Maniak003/Meteostation/Documents/IMG_20230122_160000.png

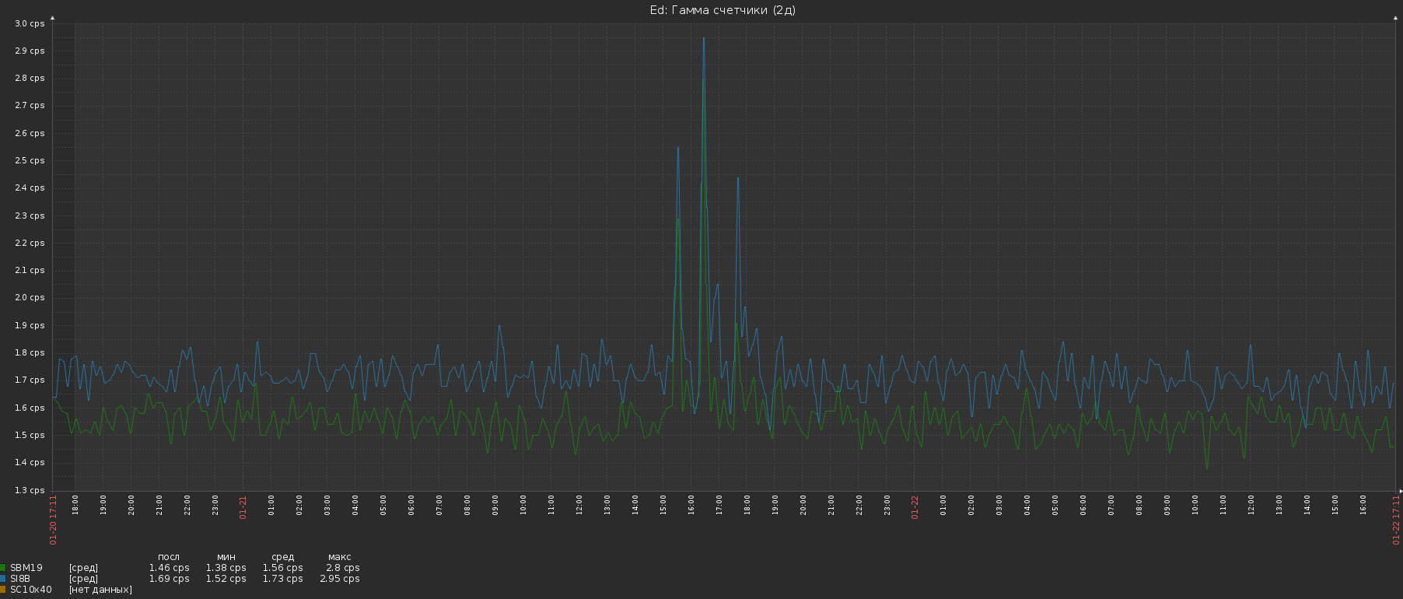
Documents/IMG_20230122_160000.png
