Maniak003/Meteostation/Documents/IMG_20230129_122235.jpg

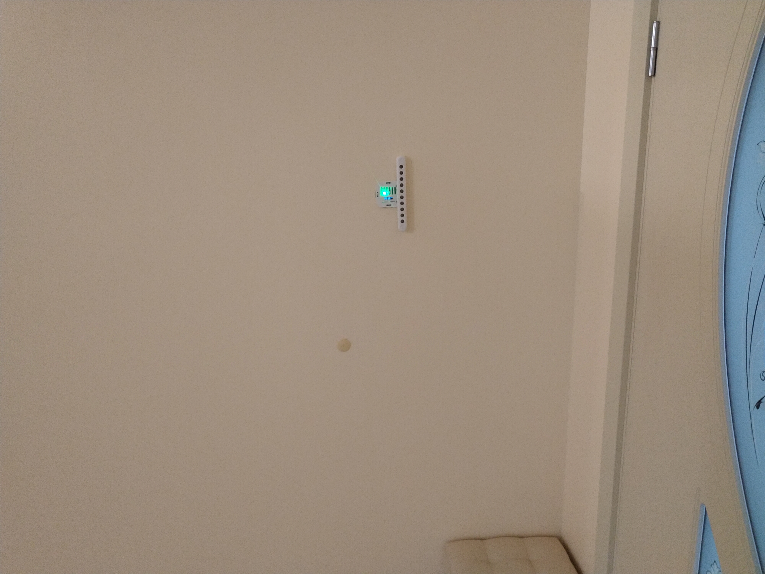
Documents/IMG_20230129_122235.jpg
