Maniak003/Meteostation/stm32cubeide/Meteostation_1.06/Core/Inc/ST7735_fonts.h

#ifndef __FONTS_H__
#define __FONTS_H__

#include <stdint.h>

typedef struct {
    const uint8_t width;
    uint8_t height;
    const uint16_t *data;
} FontDef;


extern FontDef Font_7x10;
extern FontDef Font_11x18;
extern FontDef Font_16x26;

#endif // __FONTS_H__
